antmicro/gmsl-serializer/assets/previews/layer0.png

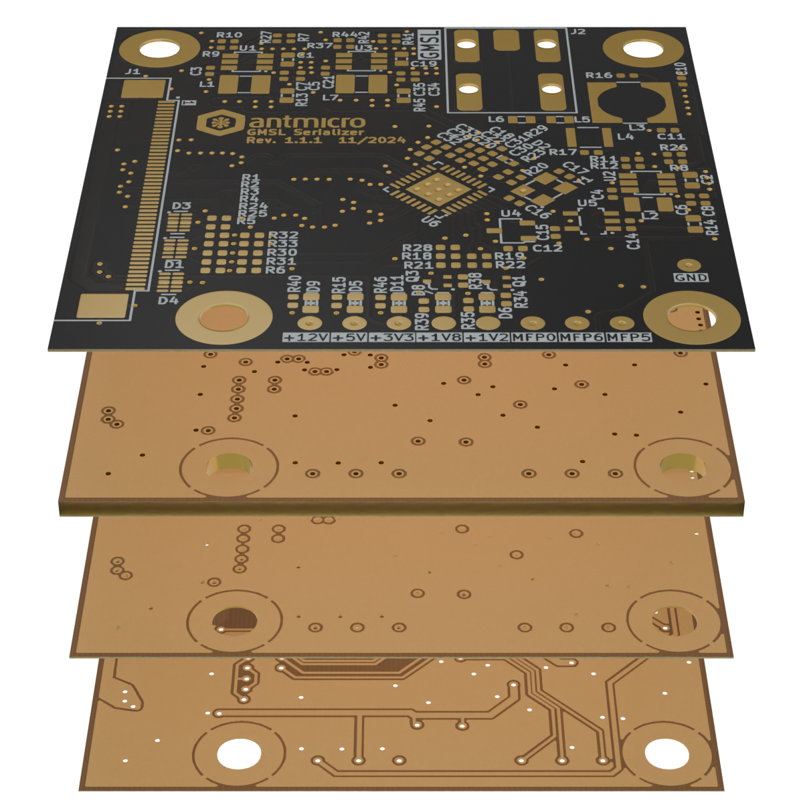
assets/previews/layer0.png
