antmicro/gmsl-serializer/assets/previews/layer0_thumbnail.png

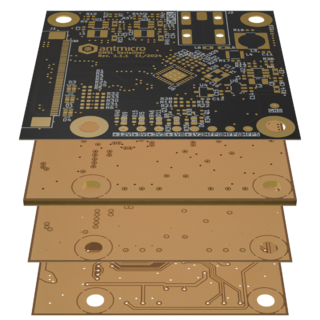
assets/previews/layer0_thumbnail.png
