antmicro/gmsl-serializer/assets/previews/layer1.webp

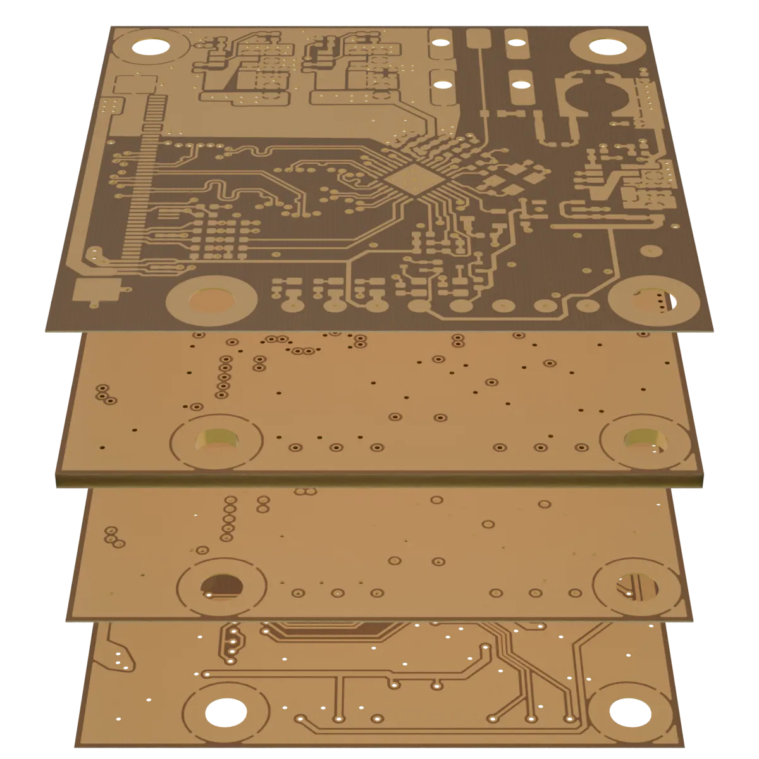
assets/previews/layer1.webp
