antmicro/gmsl-serializer/assets/previews/layer2.png

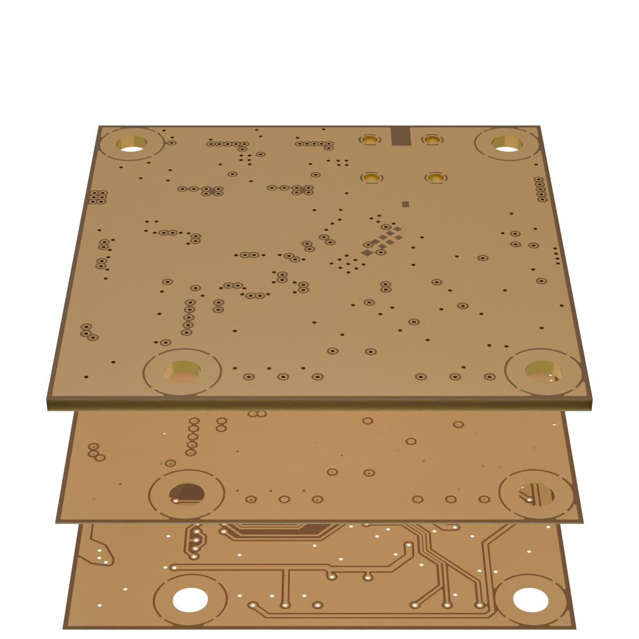
assets/previews/layer2.png
