antmicro/gmsl-serializer/assets/previews/layer2_thumbnail.webp

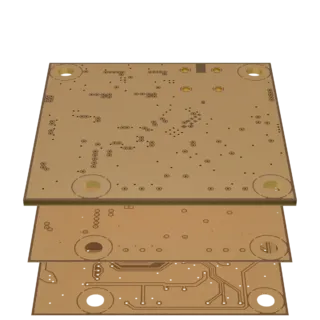
assets/previews/layer2_thumbnail.webp
