antmicro/gmsl-serializer/assets/previews/layer3.png

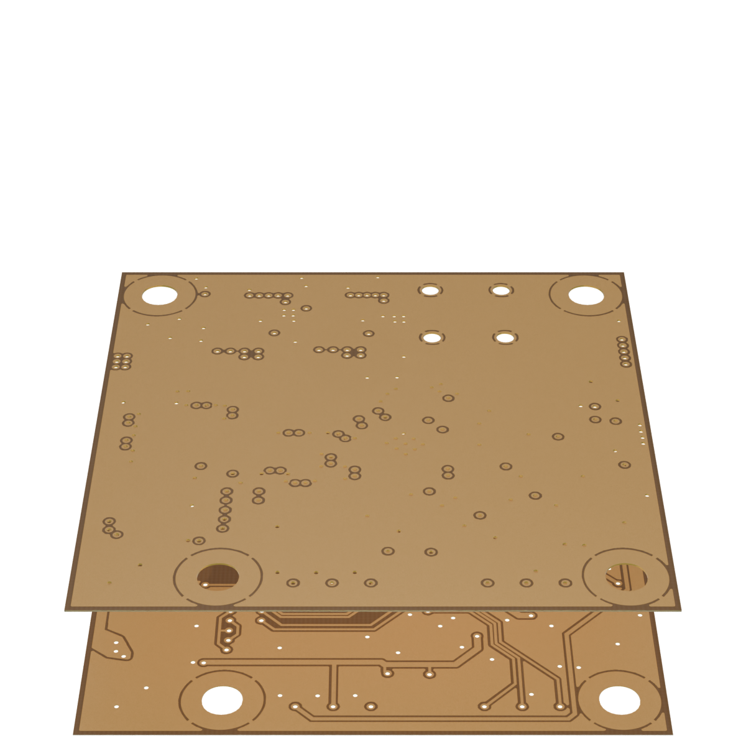
assets/previews/layer3.png
