antmicro/gmsl-serializer/assets/previews/layer4.png

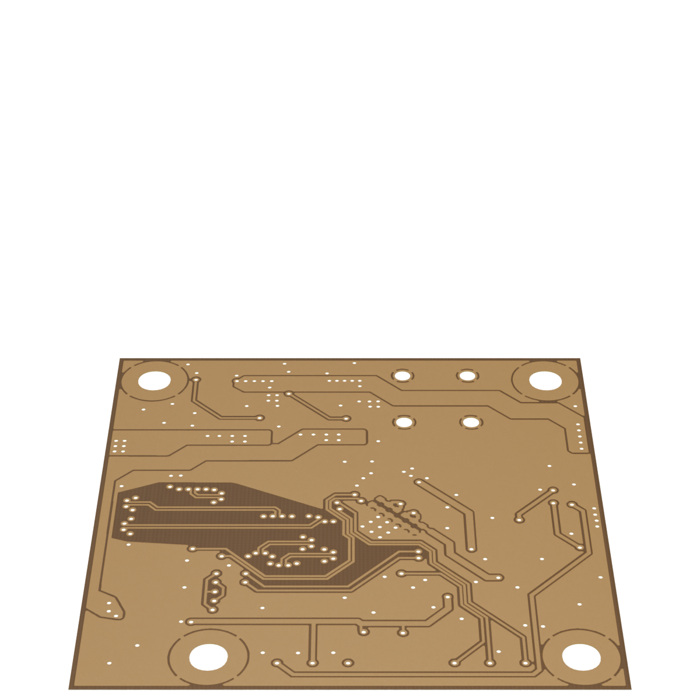
assets/previews/layer4.png
