antmicro/gmsl-serializer/assets/previews/leftB.png

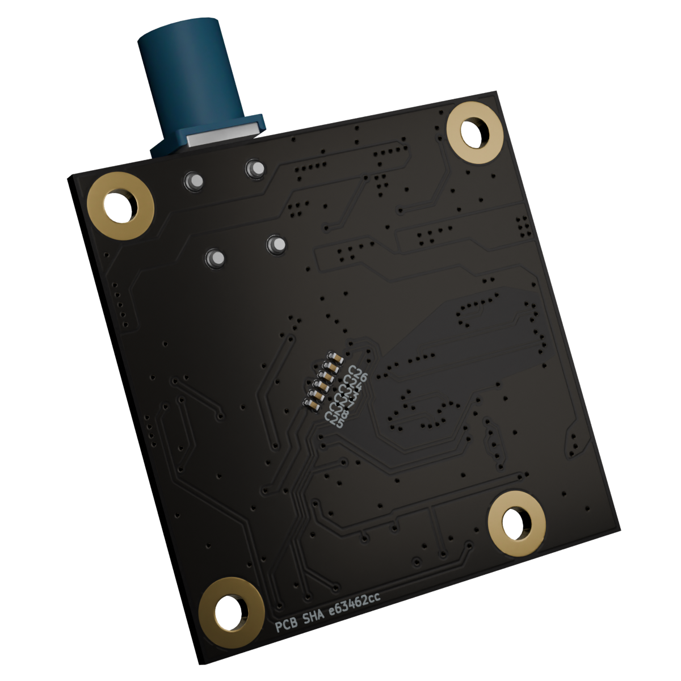
assets/previews/leftB.png
