antmicro/gmsl-serializer/assets/previews/orthoB.png

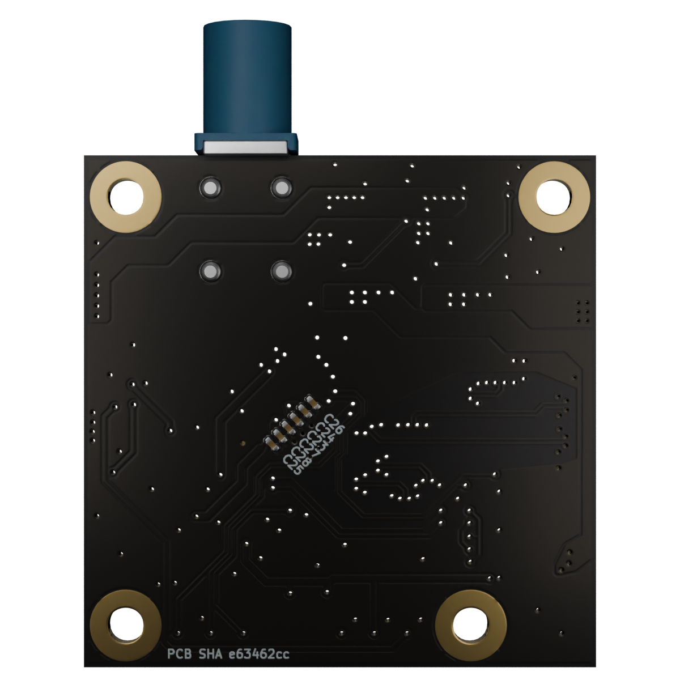
assets/previews/orthoB.png
