antmicro/gmsl-serializer/assets/previews/orthoT.png

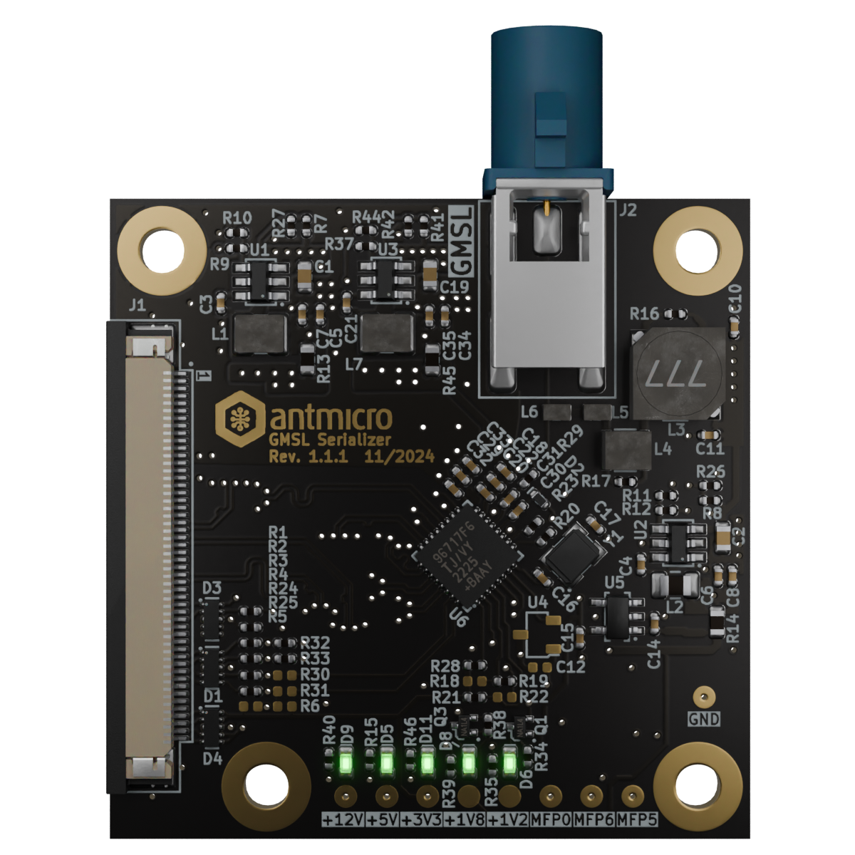
assets/previews/orthoT.png
