antmicro/gmsl-serializer/assets/previews/rightB.png

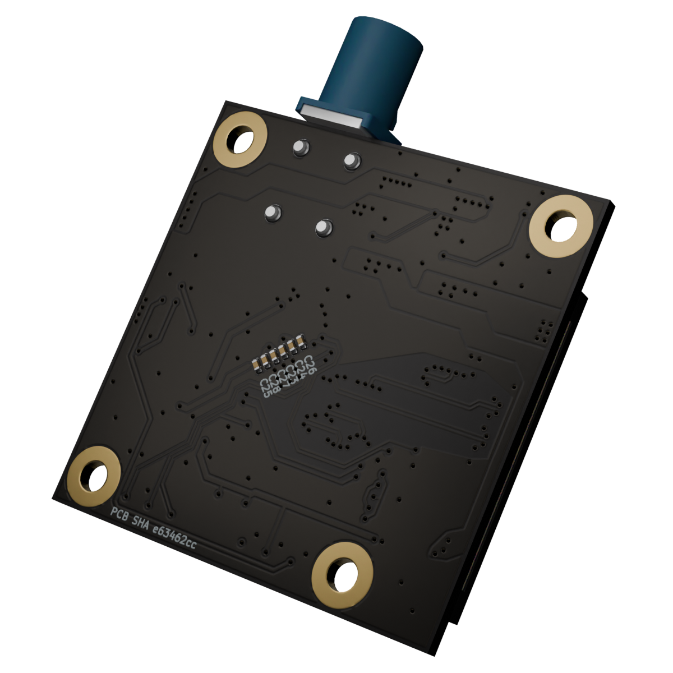
assets/previews/rightB.png
