antmicro/gmsl-serializer/assets/previews/rightT.png

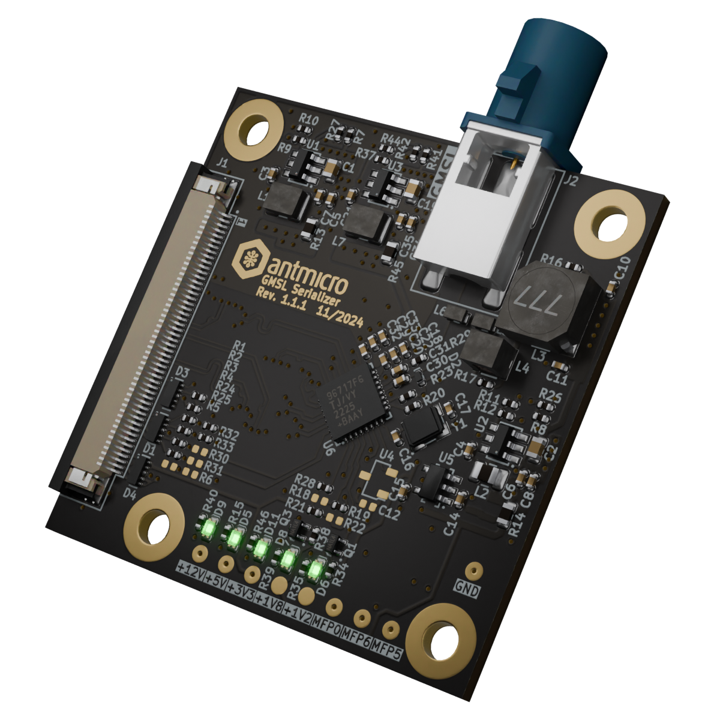
assets/previews/rightT.png
