antmicro/gmsl-serializer/assets/si/CSI_Connector_CSI.CLK_Diff/diff_delay.png

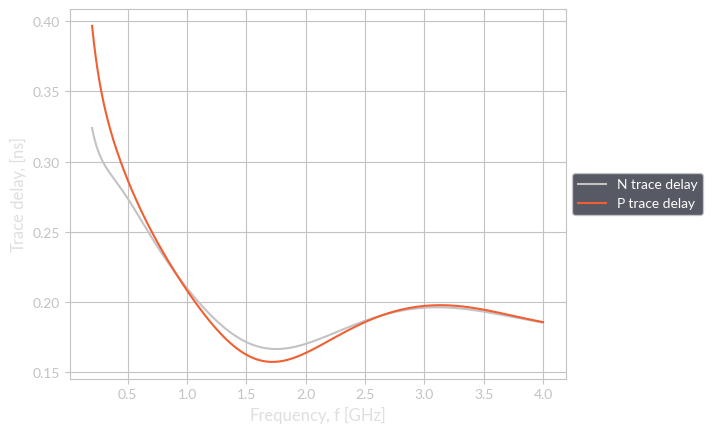
assets/si/CSI_Connector_CSI.CLK_Diff/diff_delay.png
