antmicro/gmsl-serializer/assets/si/CSI_Connector_CSI.CLK_Diff/SDD_Diff.png

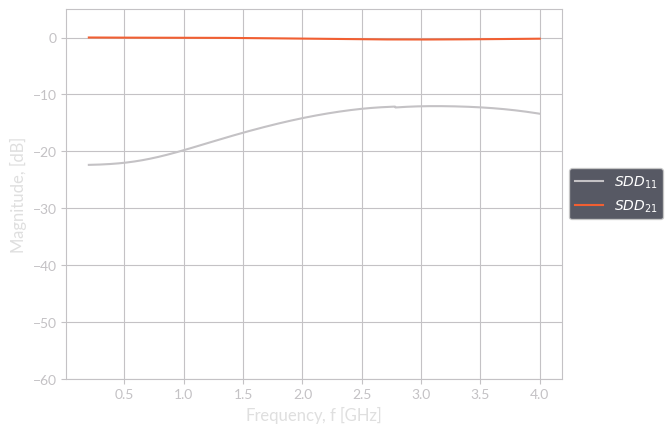
assets/si/CSI_Connector_CSI.CLK_Diff/SDD_Diff.png
