antmicro/gmsl-serializer/assets/si/CSI_Connector_CSI.CLK_Diff/Z_diff.png

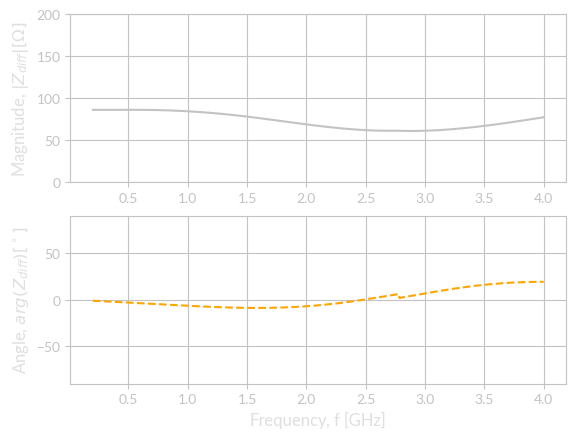
assets/si/CSI_Connector_CSI.CLK_Diff/Z_diff.png
