antmicro/gmsl-serializer/assets/si/CSI_Connector_CSI.D0_Diff/diff_delay.png

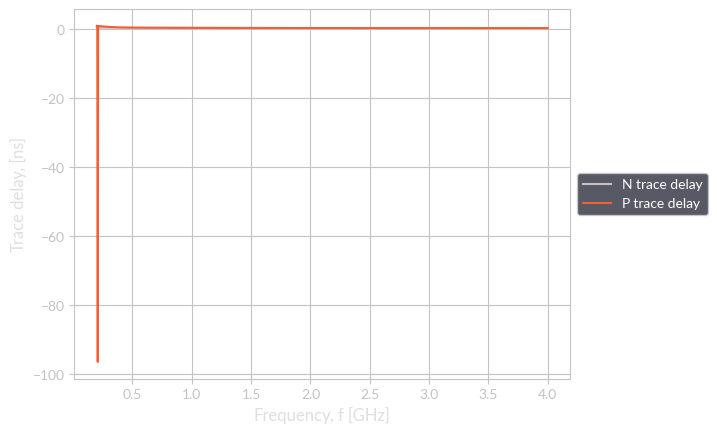
assets/si/CSI_Connector_CSI.D0_Diff/diff_delay.png
