antmicro/gmsl-serializer/assets/si/CSI_Connector_CSI.D0_Diff/s_param_and_smith_3.png

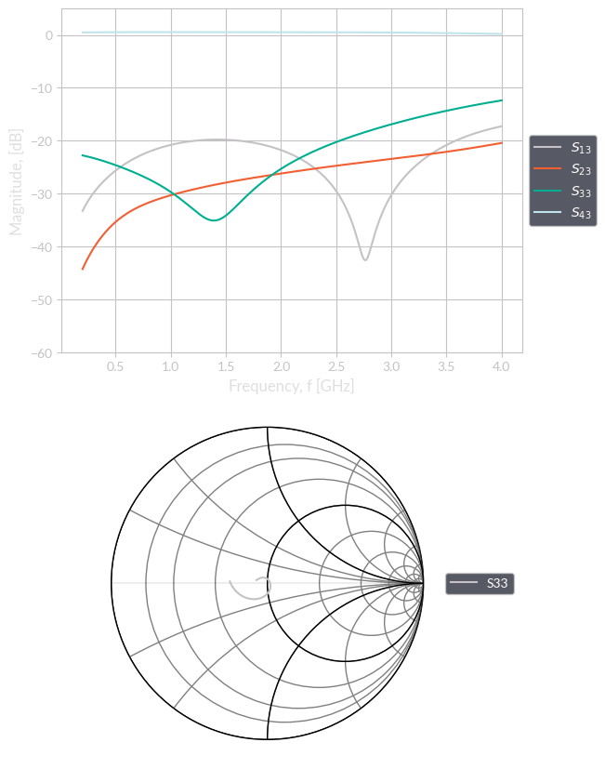
assets/si/CSI_Connector_CSI.D0_Diff/s_param_and_smith_3.png
