antmicro/gmsl-serializer/assets/si/CSI_Connector_CSI.D0_Diff/Z_3.png

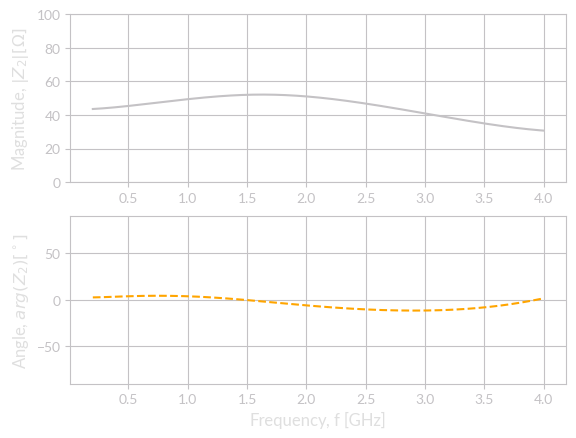
assets/si/CSI_Connector_CSI.D0_Diff/Z_3.png
