antmicro/gmsl-serializer/assets/si/CSI_Connector_CSI.D2_Diff/S_11_smith.png

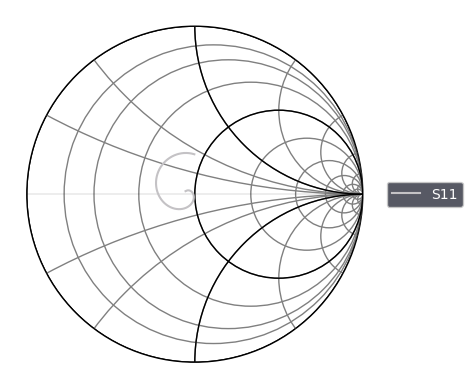
assets/si/CSI_Connector_CSI.D2_Diff/S_11_smith.png
