antmicro/gmsl-serializer/assets/si/CSI_Connector_CSI.D2_Diff/S_x3.png

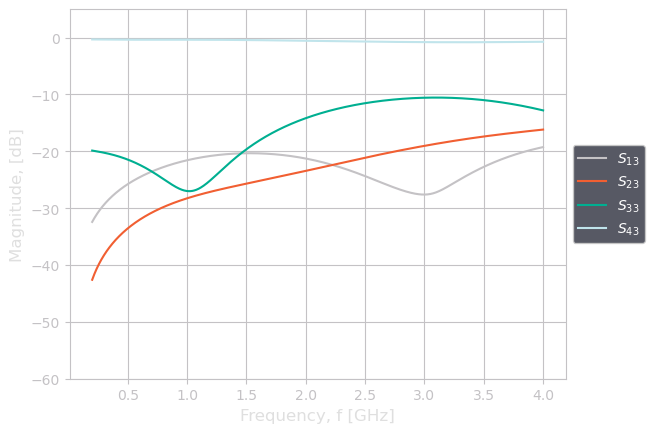
assets/si/CSI_Connector_CSI.D2_Diff/S_x3.png
