antmicro/gmsl-serializer/assets/si/CSI_Connector_CSI.D2_Diff/Z_diff.png

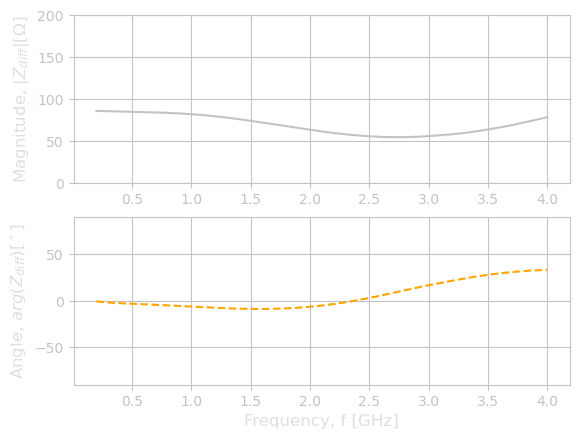
assets/si/CSI_Connector_CSI.D2_Diff/Z_diff.png
