antmicro/gmsl-serializer/assets/si/CSI_Connector_CSI.D3_Diff/diff_delay.png

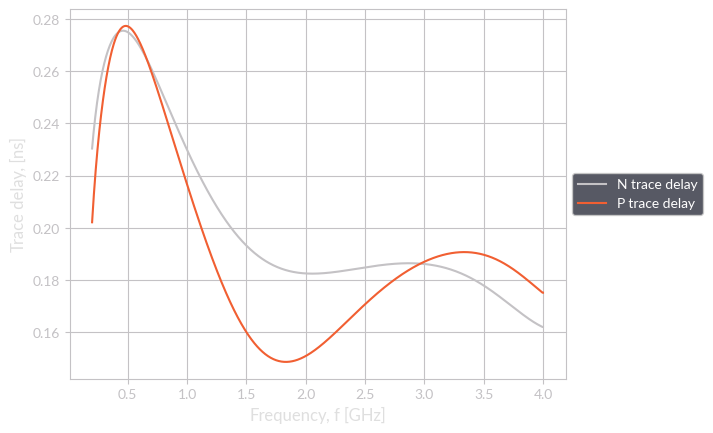
assets/si/CSI_Connector_CSI.D3_Diff/diff_delay.png
