antmicro/gmsl-serializer/assets/si/CSI_Connector_CSI.D3_Diff/s_param_and_smith_1.png

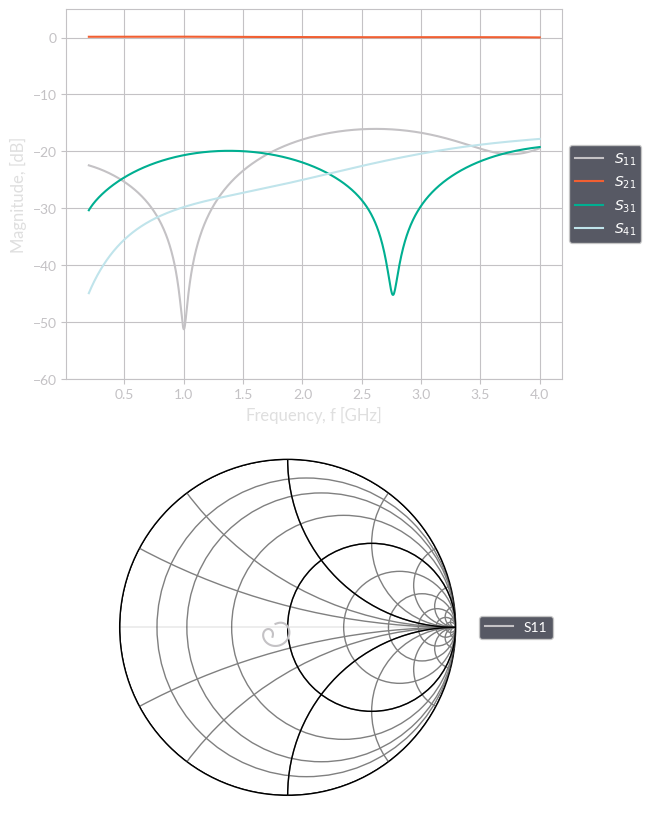
assets/si/CSI_Connector_CSI.D3_Diff/s_param_and_smith_1.png
