antmicro/gmsl-serializer/assets/si/CSI_Connector_CSI.D3_Diff/S_x1.png

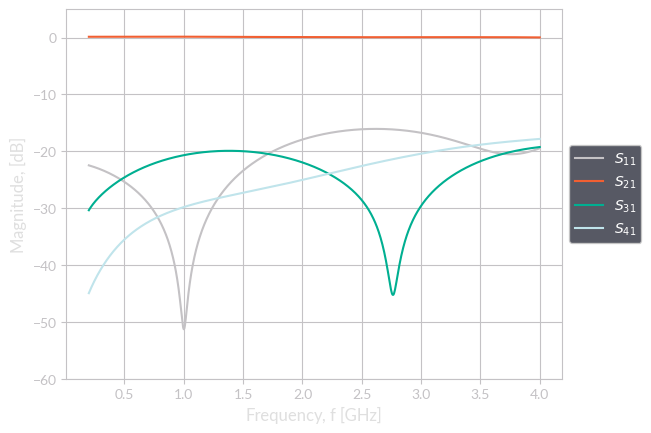
assets/si/CSI_Connector_CSI.D3_Diff/S_x1.png
