antmicro/gmsl-serializer/assets/si/CSI_Connector_CSI.D3_Diff/SDD_Diff.png

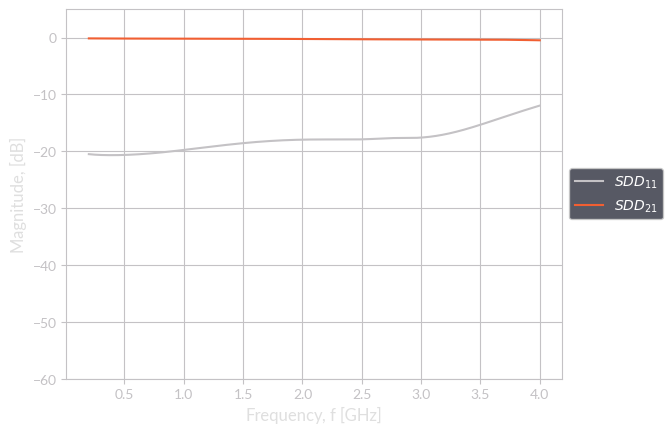
assets/si/CSI_Connector_CSI.D3_Diff/SDD_Diff.png
