antmicro/gmsl-serializer/assets/si/CSI_Connector_CSI.D3_Diff/Z_3.png

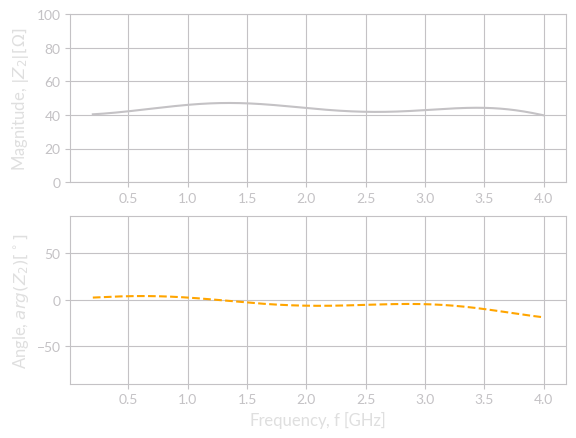
assets/si/CSI_Connector_CSI.D3_Diff/Z_3.png
