antmicro/gmsl-serializer/assets/si/GMSL_Connector_SIO_P/s_param_and_smith_1.png

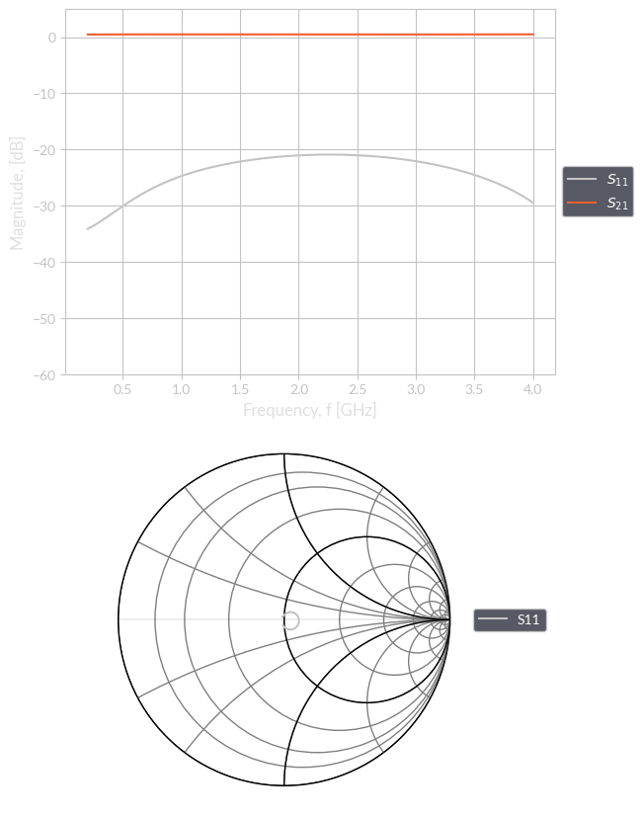
assets/si/GMSL_Connector_SIO_P/s_param_and_smith_1.png
