antmicro/gmsl-serializer/assets/si/GMSL_Connector_SIO_P/S_x1.png

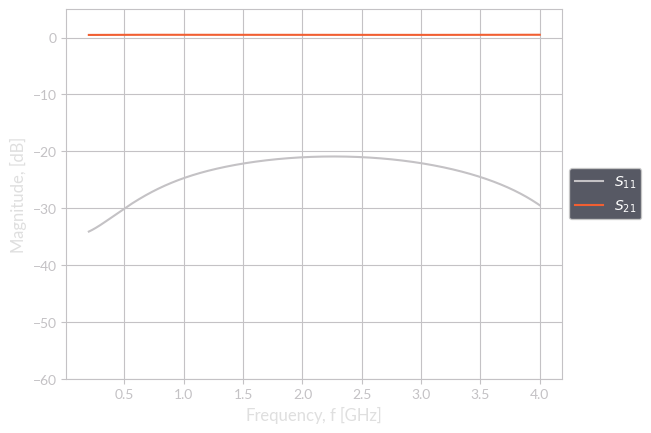
assets/si/GMSL_Connector_SIO_P/S_x1.png
