antmicro/gmsl-serializer/assets/si/Net-U6-SION/s_param_and_smith_1.png

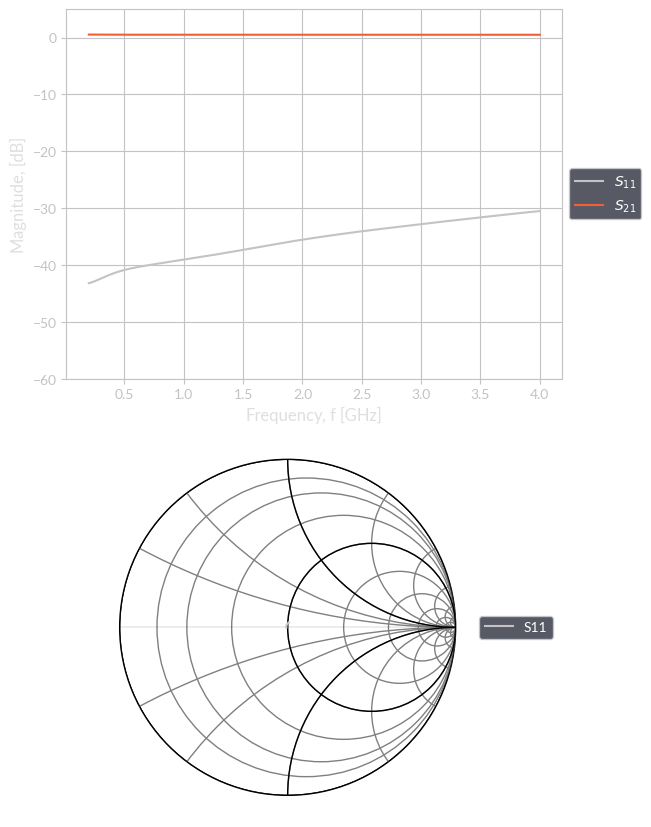
assets/si/Net-U6-SION/s_param_and_smith_1.png
