antmicro/gmsl-serializer/assets/si/Net-U6-SION/S_x1.png

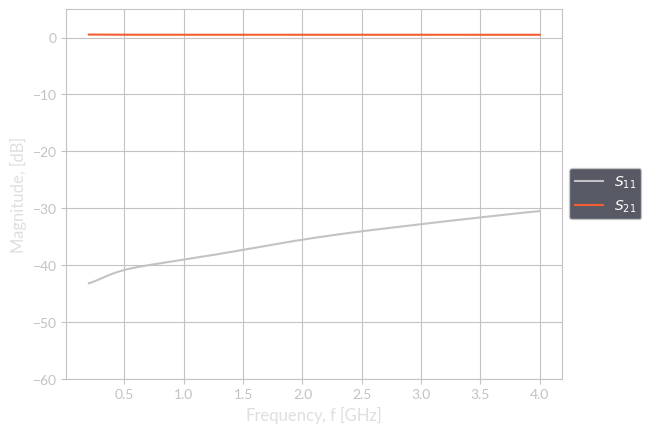
assets/si/Net-U6-SION/S_x1.png
