antmicro/gmsl-serializer/assets/si/Net-U6-SIOP/S_x1.png

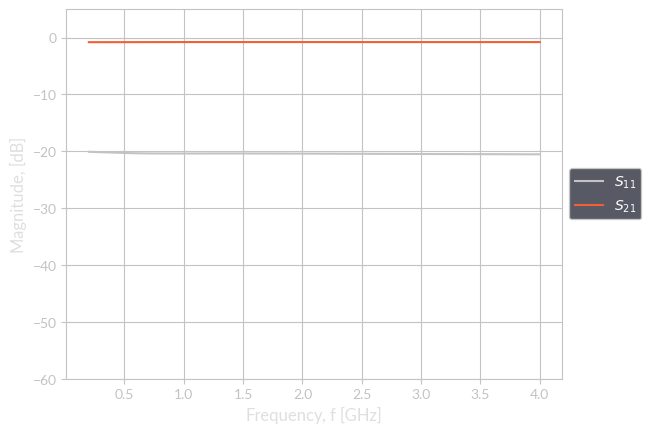
assets/si/Net-U6-SIOP/S_x1.png
