antmicro/gmsl-serializer/assets/si/Net-U6-SIOP/Z_1.png

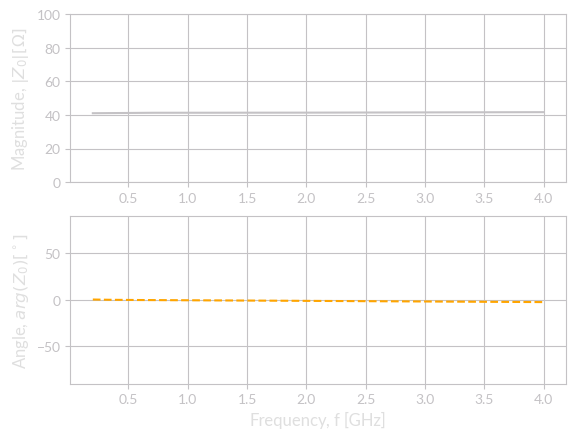
assets/si/Net-U6-SIOP/Z_1.png
