antmicro/gmsl-serializer/assets/wireframe/wireframe_descriptions_bottom.png

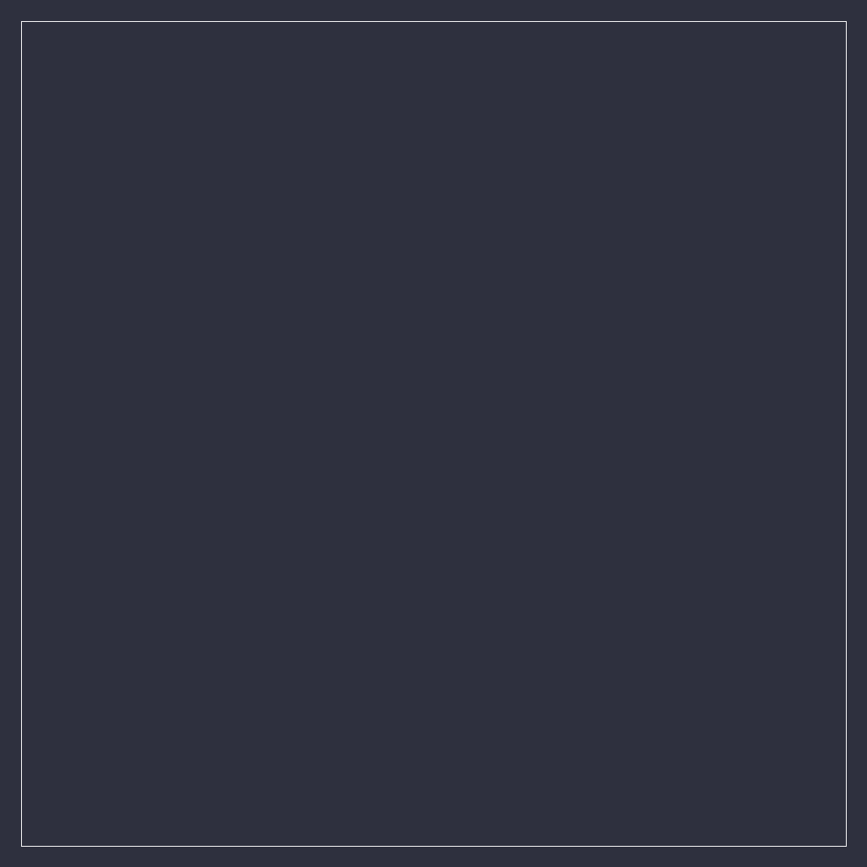
assets/wireframe/wireframe_descriptions_bottom.png
