antmicro/gmsl-serializer/assets/wireframe/wireframe_descriptions_top.png

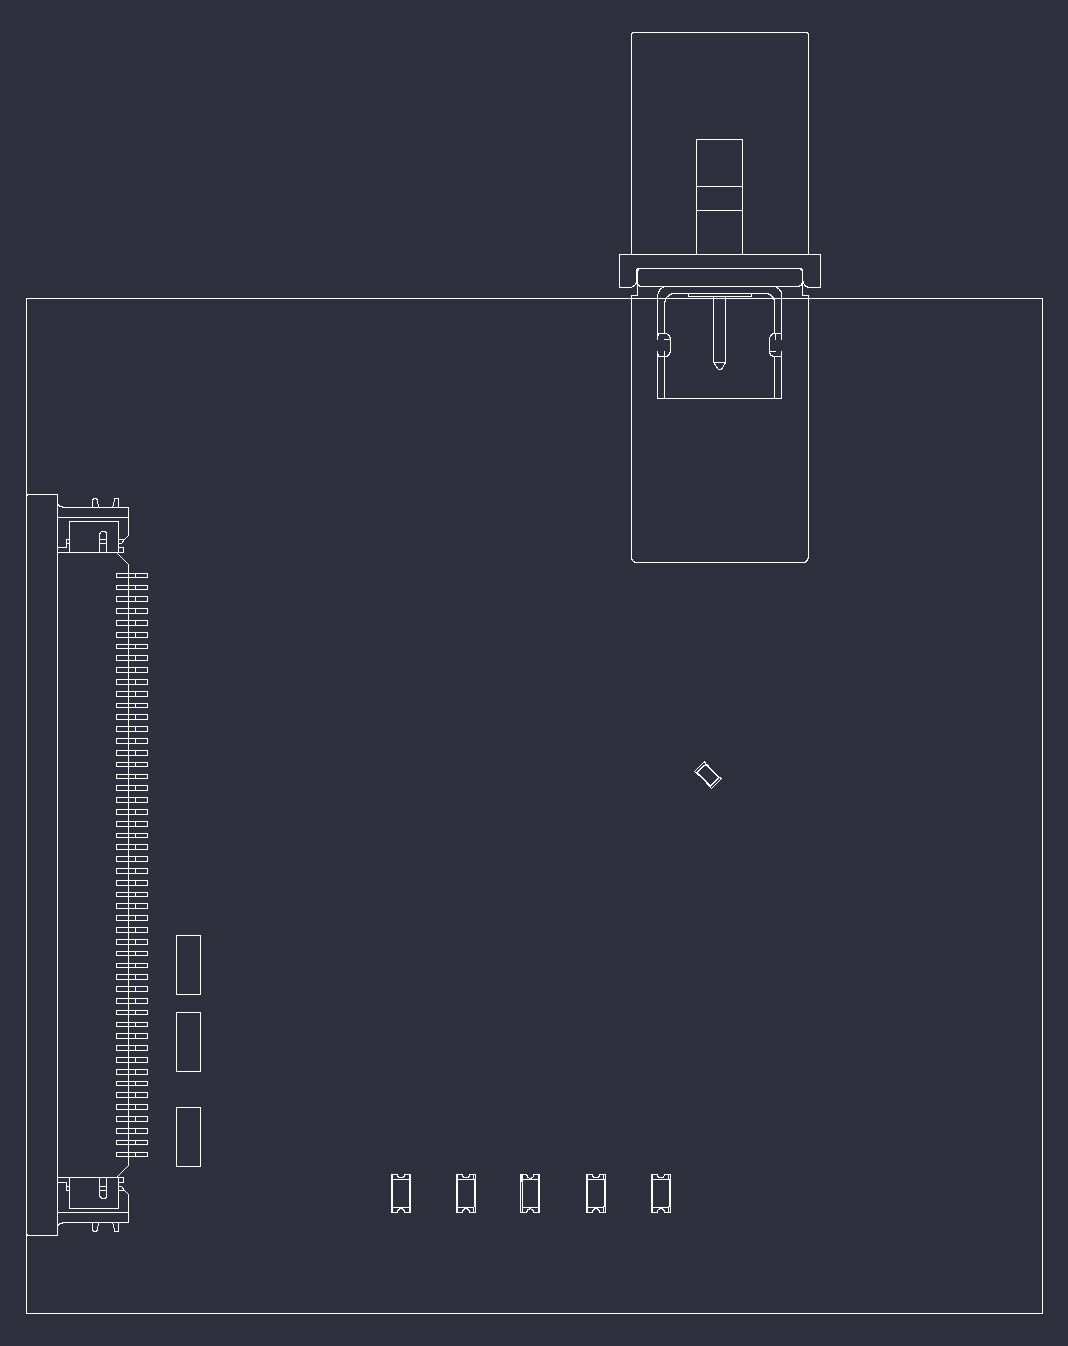
assets/wireframe/wireframe_descriptions_top.png
